nishibra/ROBO-ONE_Beginners_VisionAI/pics_elec/bnoSet.png

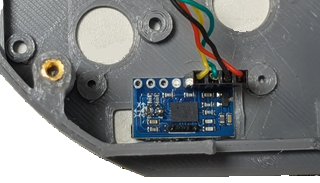
pics_elec/bnoSet.png
