nishibra/ROBO-ONE_Beginners_VisionAI/pics_elec/distance.png

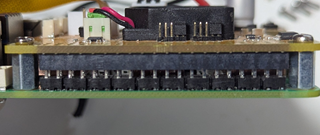
pics_elec/distance.png
