nishibra/ROBO-ONE_Beginners_VisionAI/pics_elec/led_c.png

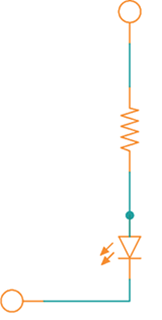
pics_elec/led_c.png
