nishibra/ROBO-ONE_Beginners_VisionAI/pics_elec/pb_led.png

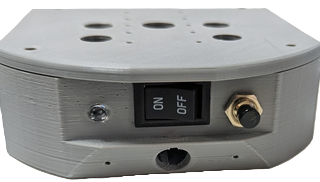
pics_elec/pb_led.png
