nishibra/ROBO-ONE_Beginners_VisionAI/pics_mech/bady_batt.jpg

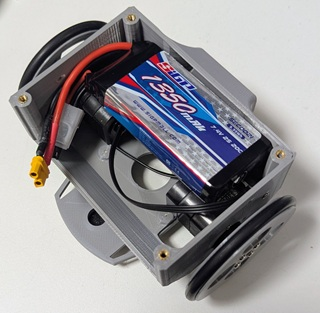
pics_mech/bady_batt.jpg
