nishibra/ROBO-ONE_Beginners_VisionAI/pics_mech/chaster.jpg

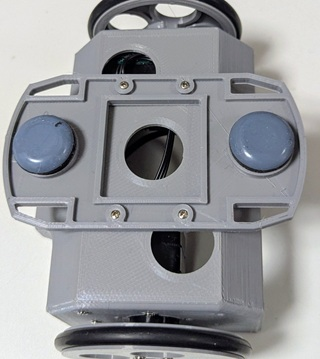
pics_mech/chaster.jpg
