nishibra/ROBO-ONE_Beginners_VisionAI/pics_mech/cpu_and_case.jpg

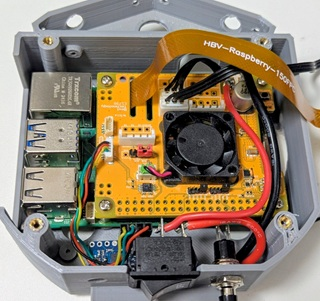
pics_mech/cpu_and_case.jpg
