nishibra/ROBO-ONE_Beginners_VisionAI/pics_mech/pi5_Vision_Asy_3D.jpg

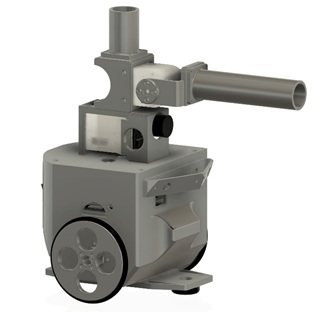
pics_mech/pi5_Vision_Asy_3D.jpg
