nishibra/ROBO-ONE_Beginners_VisionAI/pics_mech/set_battery.jpg

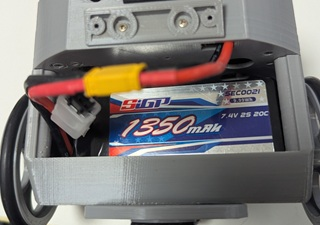
pics_mech/set_battery.jpg
