nishibra/ROBO-ONE_Beginners_VisionAI/pics_prog/cont.png

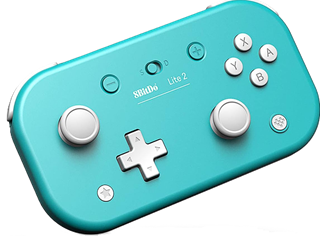
pics_prog/cont.png
