nishibra/ROBO-ONE_Beginners_VisionAI/pics_prog/pi4_1.png

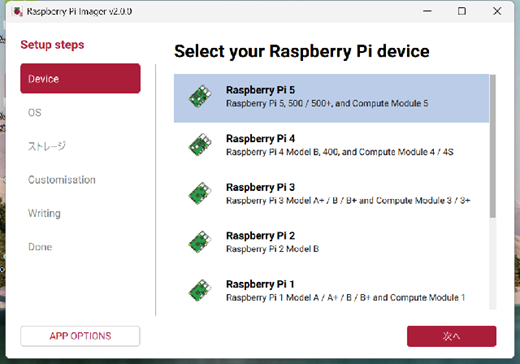
pics_prog/pi4_1.png
