nishibra/ROBO-ONE_Beginners_VisionAI/stl/CPU_case.stl

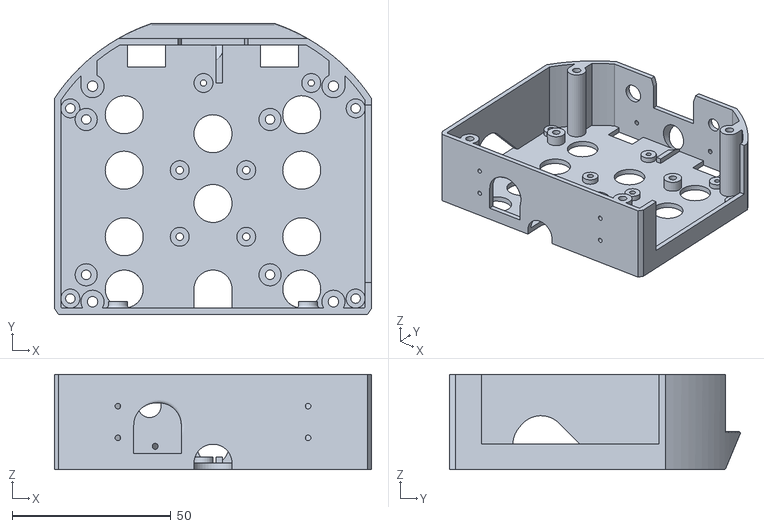
[picture p71: CAD file, 2026-04-21]
stl/CPU_case.stl
100.0 x 91.7 x 30.0
