nishibra/ROBO-ONE_Beginners_VisionAI/stl/Battery_cover.stl

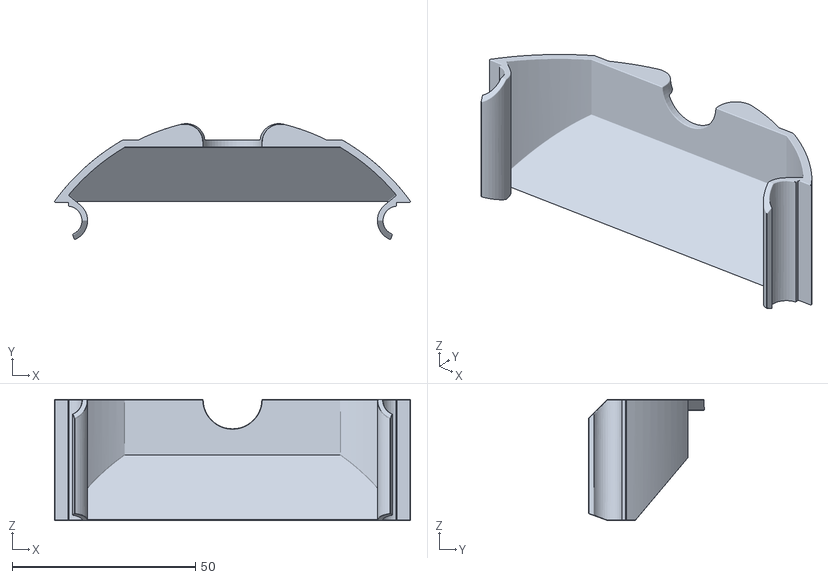
[picture p72: CAD file, 2026-04-21]
stl/Battery_cover.stl
97.1 x 31.6 x 33.0
