nishibra/ROBO-ONE_Beginners_VisionAI/stl/psd2_bkt.stl

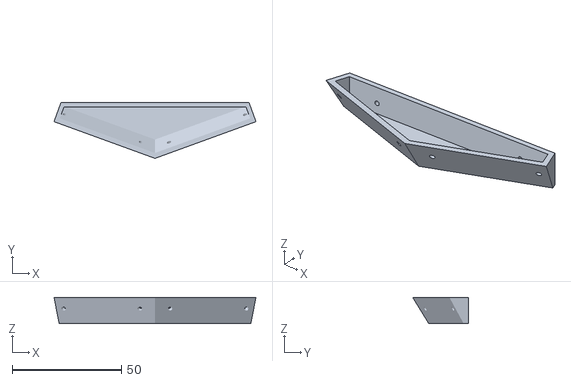
[picture p73: CAD file, 2026-04-21]
stl/psd2_bkt.stl
92.3 x 25.5 x 12.0
