nishibra/ROBO-ONE_Beginners_VisionAI/stl/Psd1_bkt v6.stl

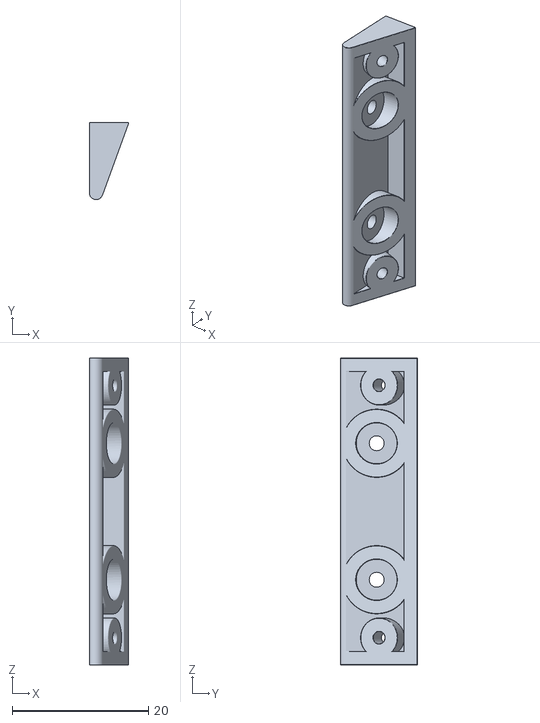
[picture p74: CAD file, 2026-03-15]
stl/Psd1_bkt v6.stl
5.78 x 11.3 x 45.0
