nishibra/ROBO-ONE_Beginners_VisionAI/stl/Arm v1.stl

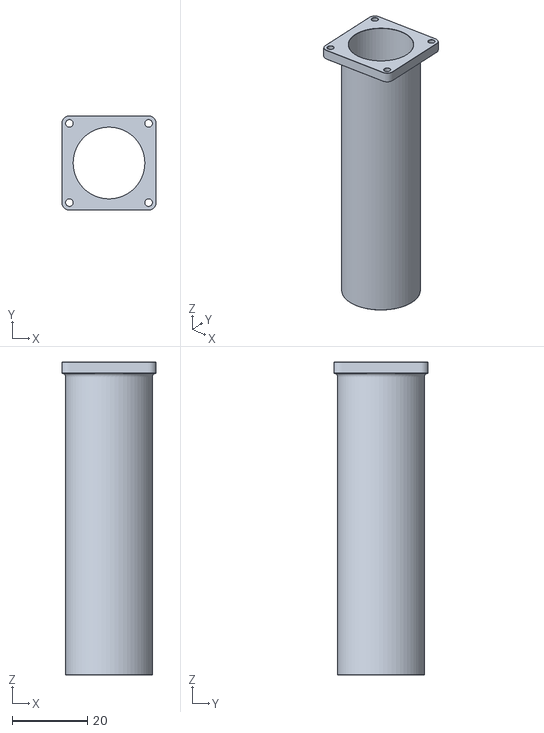
[picture p75: CAD file, 2026-03-15]
stl/Arm v1.stl
25.0 x 25.0 x 83.0
