nishibra/ROBO-ONE_Beginners_VisionAI/stl/Head v1.stl

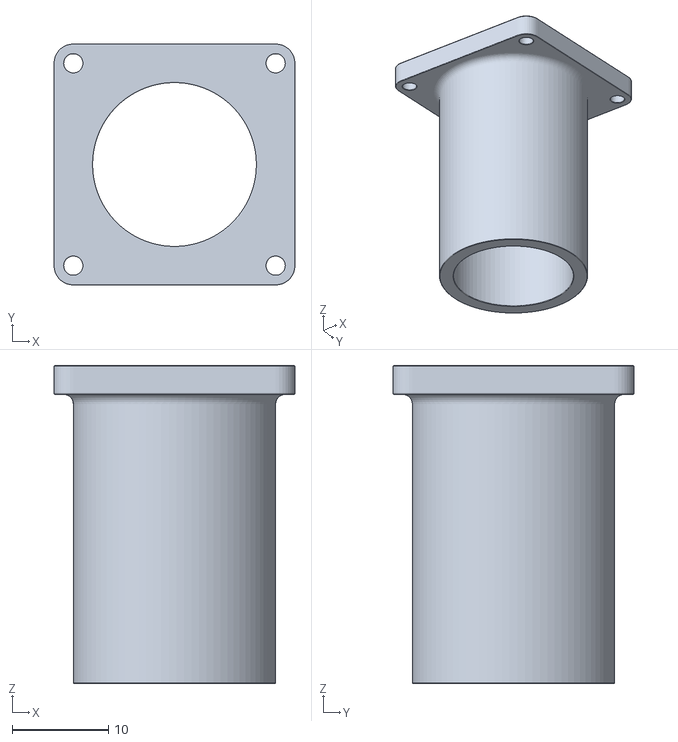
[picture p76: CAD file, 2026-03-15]
stl/Head v1.stl
25.0 x 25.0 x 33.0
